MaayZz/Urban-Glow-Grid/image/IMG_7003.jpg

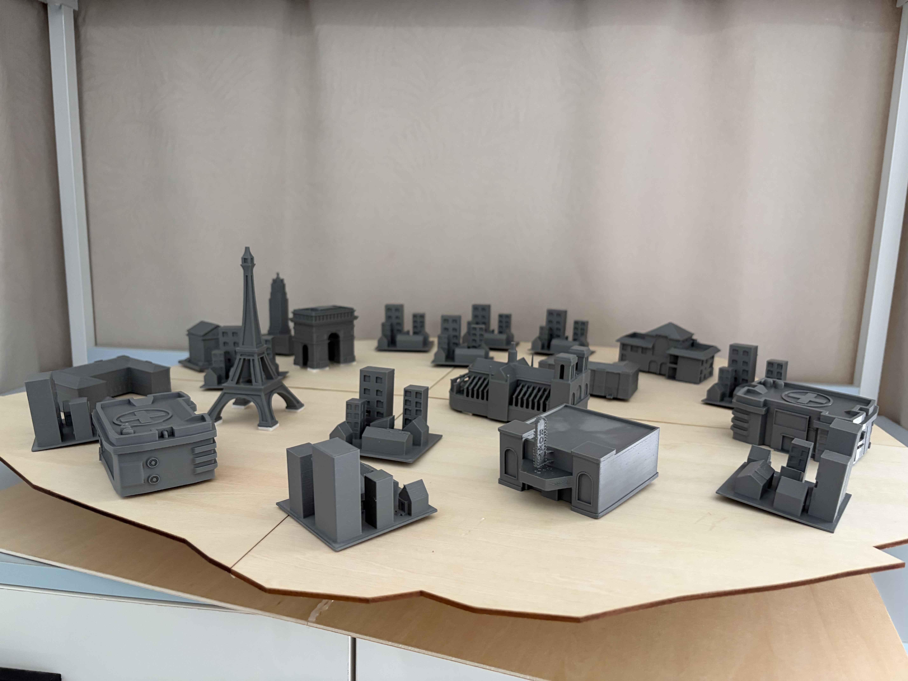
image/IMG_7003.jpg
