MaayZz/Urban-Glow-Grid/image/IMG_7004.jpg

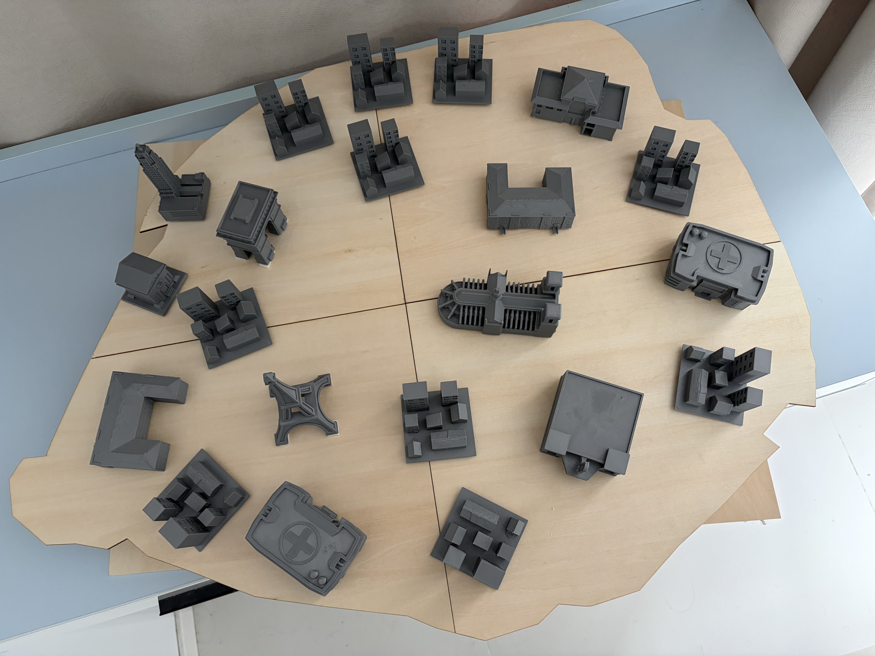
image/IMG_7004.jpg
