MaayZz/Urban-Glow-Grid/image/IMG_7005.jpg

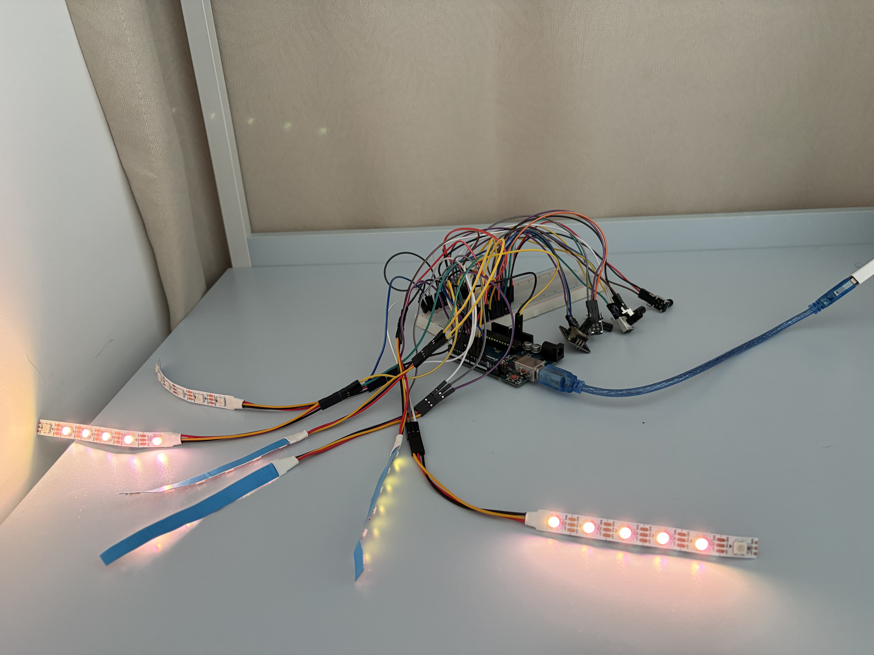
image/IMG_7005.jpg
