MaayZz/Urban-Glow-Grid/image/IMG_7006.jpg

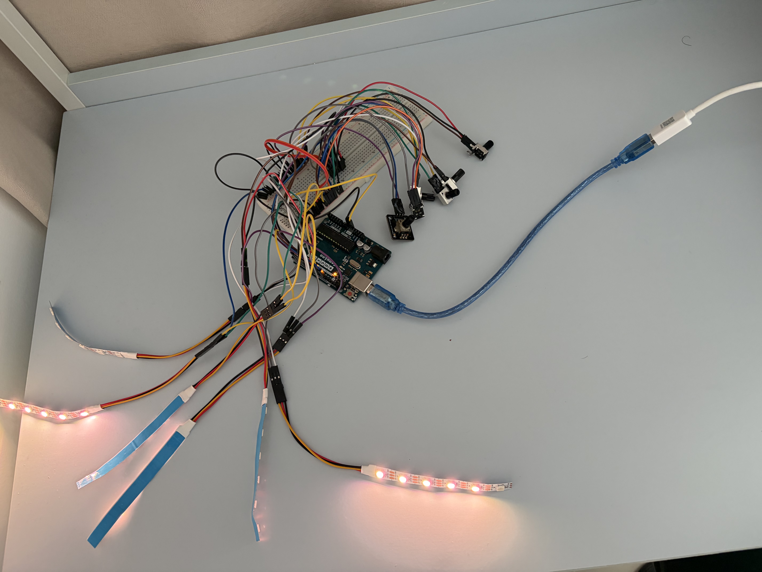
image/IMG_7006.jpg
